lonesoulsurfer/Freaq_FM_Synth-Modular_Synth_Version/Eagle Files/Freaq.sch

## EAGLE design Eagle Files/Freaq.sch (2025-05-07, an earlier design)

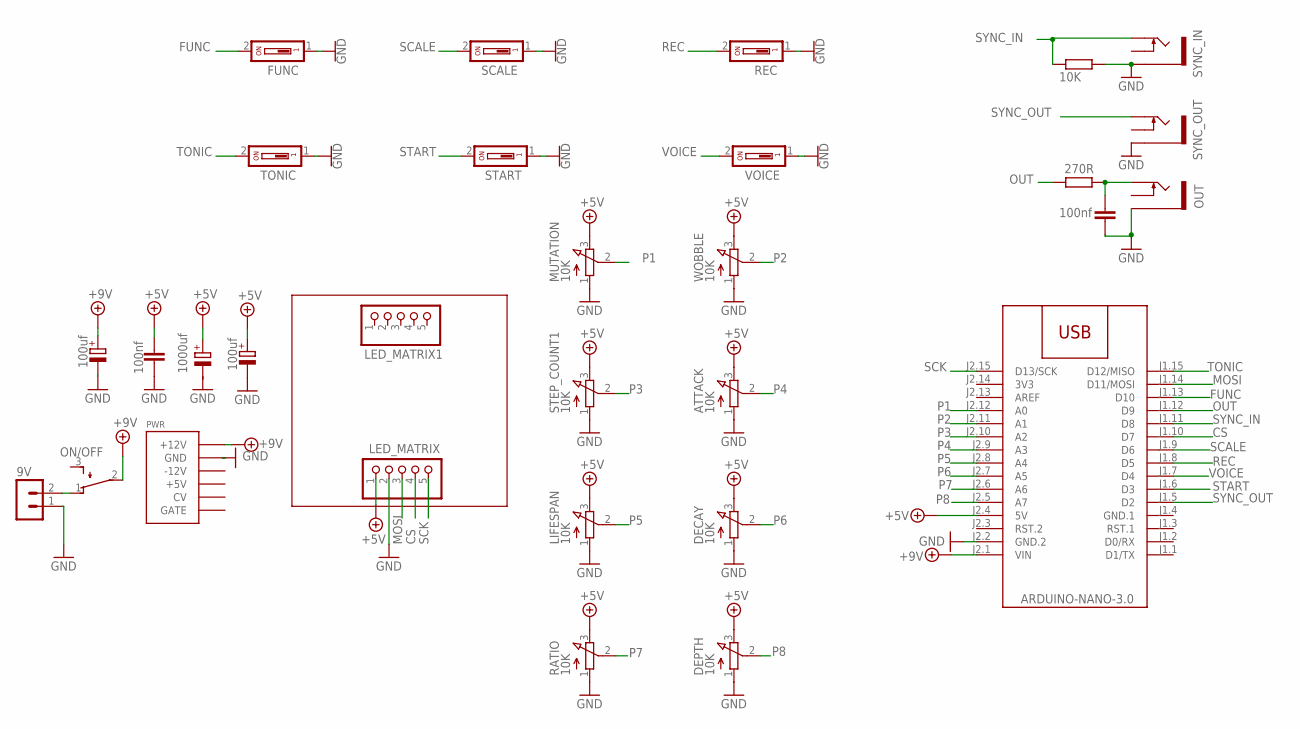
[picture p5: schematic Freaq.sch]

Parts:
9V: B2B-PH-K-S
ATTACK: 10K; EVUFXL
C1, C4: 100nf; C050-024X044
C2, C3: 100uf; E2-5
C5: 1000uf; E2,5-6E
DECAY: 10K; EVUFXL
DEPTH: 10K; EVUFXL
FUNC: DS01; DS-01
LED_MATRIX, LED_MATRIX1: PINHD-1X5; 1X05
LIFESPAN: 10K; EVUFXL
M1: ARDUINO-NANO-3.0
MUTATION: 10K; EVUFXL
ON/OFF: TL32PO; TL3XPO
OUT: THONKICONNNEW; WQP-PJ301M-12_JACK
PWR: POWER; POWER_16
R7: 10K; 0207/10
R8: 270R; 0207/10
RATIO: 10K; EVUFXL
REC: DS01; DS-01
SCALE: DS01; DS-01
START: DS01; DS-01
STEP_COUNT1: 10K; EVUFXL
SYNC_IN: THONKICONNNEW; WQP-PJ301M-12_JACK
SYNC_OUT: THONKICONNNEW; WQP-PJ301M-12_JACK
TONIC: DS01; DS-01
VOICE: DS01; DS-01
WOBBLE: 10K; EVUFXL

Connections:
+5V: ATTACK.3 (E), C1.1, C2.+, C5.+, DECAY.3 (E), DEPTH.3 (E), LED_MATRIX.1, LIFESPAN.3 (E), M1.J2.4 (5V), MUTATION.3 (E), RATIO.3 (E), STEP_COUNT1.3 (E), WOBBLE.3 (E)
+9V: C3.+, M1.J2.1 (VIN), ON/OFF.2, PWR.9 (+12V)
CS: LED_MATRIX.4, M1.J1.10 (D7)
FUNC: FUNC.2, M1.J1.13 (D10)
GND: 9V.1, ATTACK.1 (A), C1.2, C2.-, C3.-, C4.2, DECAY.1 (A), DEPTH.1 (A), FUNC.1, LED_MATRIX.2, LIFESPAN.1 (A), M1.J2.2 (GND.2), MUTATION.1 (A), OUT.P$3_SLEEVE (SLEEVE), PWR.3 (GND), R7.2, RATIO.1 (A), REC.1, SCALE.1, START.1, STEP_COUNT1.1 (A), SYNC_IN.P$3_SLEEVE (SLEEVE), SYNC_OUT.P$3_SLEEVE (SLEEVE), TONIC.1, VOICE.1, WOBBLE.1 (A)
MOSI: LED_MATRIX.3, M1.J1.14 (D11/MOSI)
unnamed: 9V.2, ON/OFF.1 (O)
unnamed: C4.1, OUT.P$1_TIP (TIP), R8.2
OUT: M1.J1.12 (D9), R8.1
P1: M1.J2.12 (A0), MUTATION.2 (S)
P2: M1.J2.11 (A1), WOBBLE.2 (S)
P3: M1.J2.10 (A2), STEP_COUNT1.2 (S)
P4: ATTACK.2 (S), M1.J2.9 (A3)
P5: LIFESPAN.2 (S), M1.J2.8 (A4)
P6: DECAY.2 (S), M1.J2.7 (A5)
P7: M1.J2.6 (A6), RATIO.2 (S)
P8: DEPTH.2 (S), M1.J2.5 (A7)
REC: M1.J1.8 (D5), REC.2
SCALE: M1.J1.9 (D6), SCALE.2
SCK: LED_MATRIX.5, M1.J2.15 (D13/SCK)
START: M1.J1.6 (D3), START.2
SYNC_IN: M1.J1.11 (D8), R7.1, SYNC_IN.P$1_TIP (TIP)
SYNC_OUT: M1.J1.5 (D2), SYNC_OUT.P$1_TIP (TIP)
TONIC: M1.J1.15 (D12/MISO), TONIC.2
VOICE: M1.J1.7 (D4), VOICE.2
